ArthorH/Original-LF-Timegate/Edge-detector-simulation/Wykrywacz_zbocza_wzr.asc

C1: cap; 10nf
C2: cap; 10µf
C3: cap; 10nf
C4: cap; 1nf
Q1: npn; BC547C
Q2: npn; BC547C
R1: res; 220k
R2: res; 50k
R3: res; 10k
R4: res; 100k
R5: res; 10Meg
R6: res; 10k
R8: res; 10k
U1: LM2901
V1: voltage; PULSE(0 5 100us 100us 100us 10ms 20ms); Rser=50
V2: voltage; 5
Named nets: +5, 0, out
.tran 30ms
